andrewb435/gameKey-STL/Thumb Cluster/gameKey_Thumb_Rail.stl

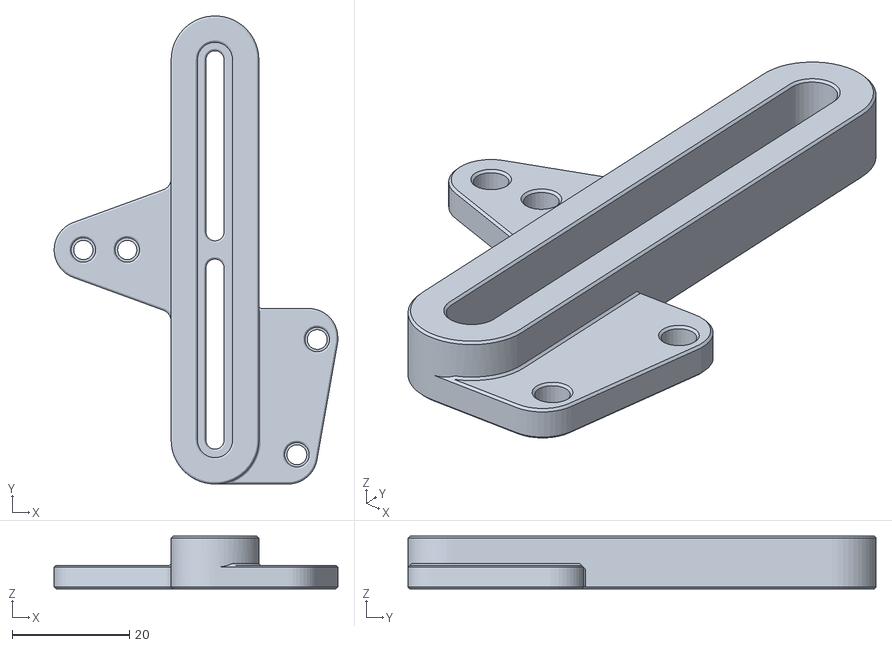
[picture p16: CAD file, 2022-02-08]
Thumb Cluster/gameKey_Thumb_Rail.stl
48.5 x 80.0 x 9.00
