andrewb435/gameKey-STL/Base & Palmrest/gameKey_Finger_SliderMount_Index.stl

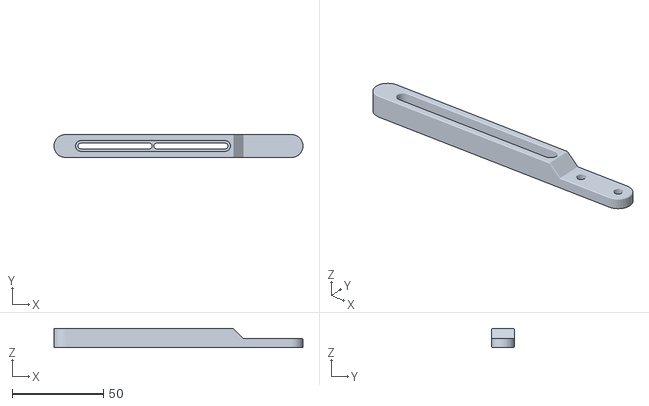
[picture p17: CAD file, 2022-02-08]
Base & Palmrest/gameKey_Finger_SliderMount_Index.stl
136.8 x 12.6 x 10.5
