andrewb435/gameKey-STL/Fingers/gameKey_Finger_Addon_IndexB.stl

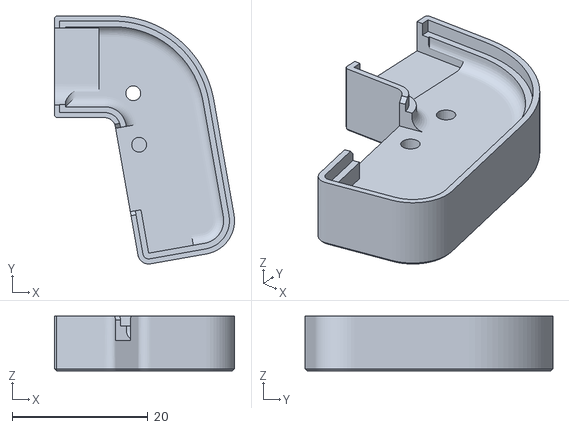
[picture p18: CAD file, 2022-02-08]
Fingers/gameKey_Finger_Addon_IndexB.stl
26.6 x 36.6 x 8.10
