andrewb435/gameKey-STL/Base & Palmrest/gameKey_Finger_SliderMount_Middle.stl

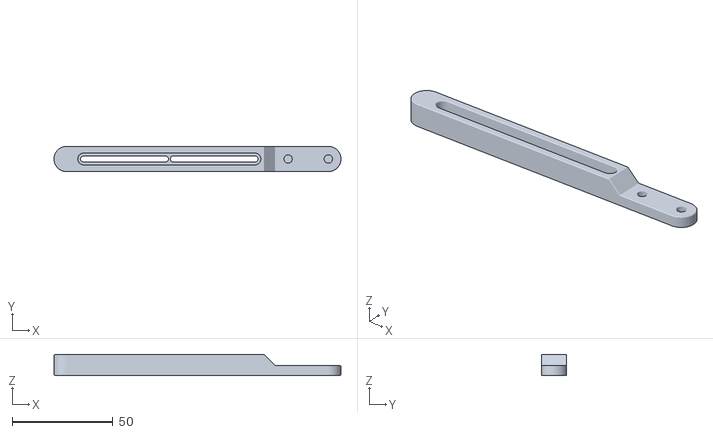
[picture p19: CAD file, 2022-02-08]
Base & Palmrest/gameKey_Finger_SliderMount_Middle.stl
142.6 x 12.6 x 10.5
