andrewb435/gameKey-STL/Fingers/gameKey_Finger_Addon_IndexA.stl

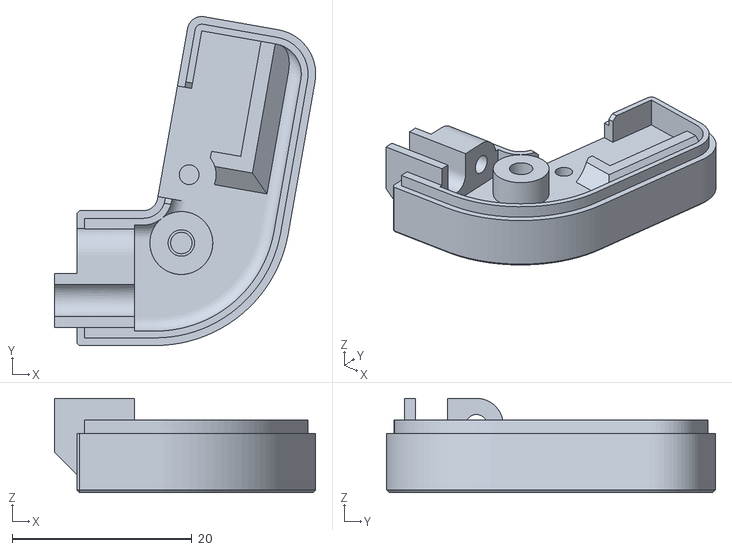
[picture p20: CAD file, 2022-02-08]
Fingers/gameKey_Finger_Addon_IndexA.stl
29.1 x 36.6 x 10.5
