andrewb435/gameKey-STL/Thumb Cluster/gameKey_ThumbCluster_JS5208-Stick.stl

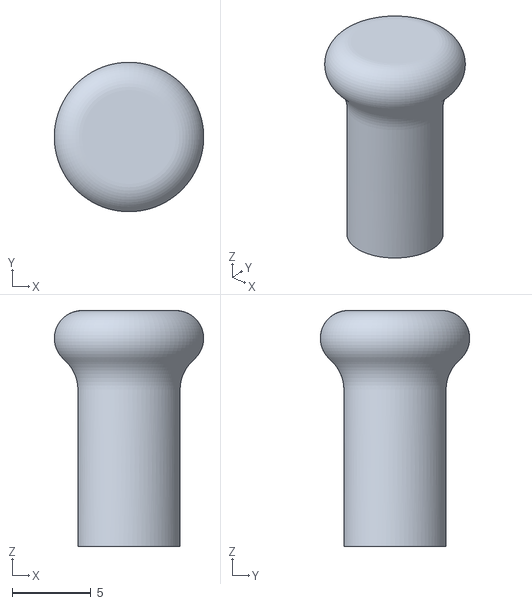
[picture p21: CAD file, 2022-02-08]
Thumb Cluster/gameKey_ThumbCluster_JS5208-Stick.stl
9.49 x 9.50 x 15.0
