andrewb435/gameKey-STL/Base & Palmrest/gameKey_Finger_SliderMount_Ring.stl

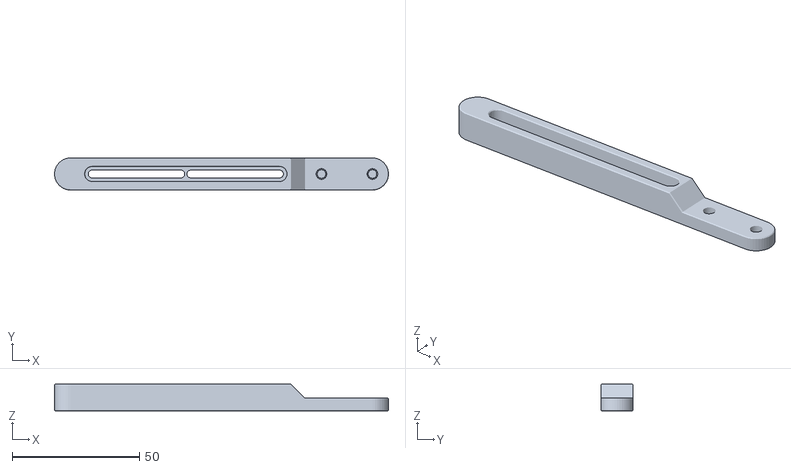
[picture p22: CAD file, 2022-02-08]
Base & Palmrest/gameKey_Finger_SliderMount_Ring.stl
131.1 x 12.6 x 10.5
