andrewb435/gameKey-STL/Thumb Cluster/gameKey_ThumbCluster_Body.stl

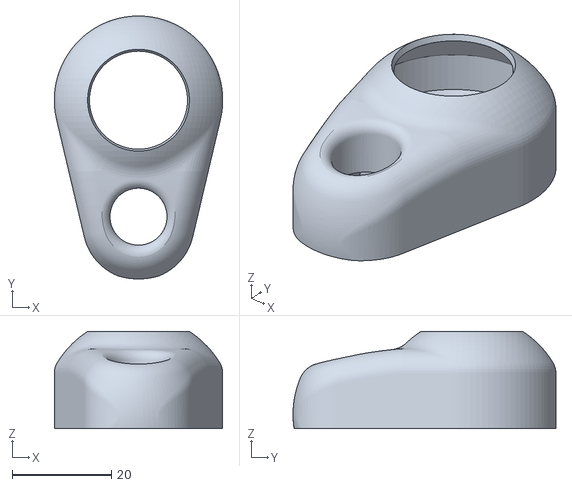
[picture p23: CAD file, 2022-02-08]
Thumb Cluster/gameKey_ThumbCluster_Body.stl
34.0 x 53.1 x 19.6
