andrewb435/gameKey-STL/Thumb Cluster/gameKey_ThumbCluster_Back.stl

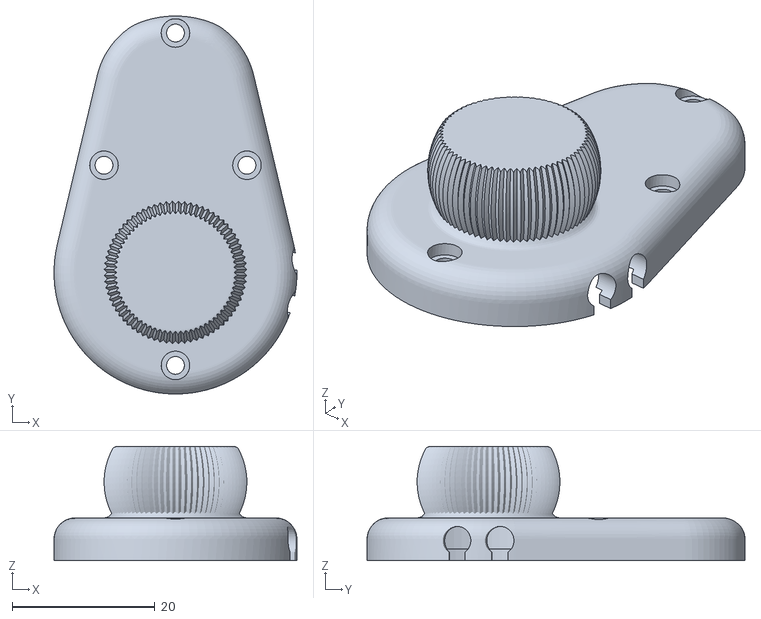
[picture p24: CAD file, 2022-02-08]
Thumb Cluster/gameKey_ThumbCluster_Back.stl
34.0 x 52.9 x 16.0
