andrewb435/gameKey-STL/Fingers/gameKey_Finger_PaddleLarge.stl

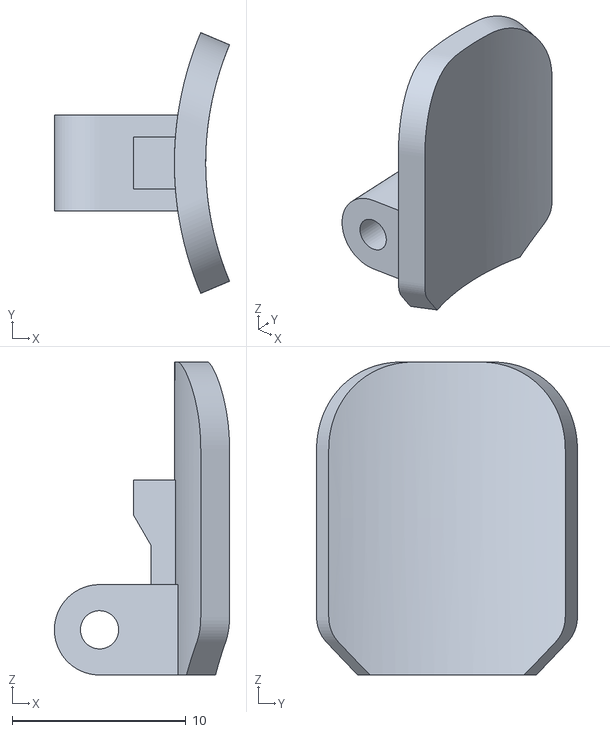
[picture p25: CAD file, 2022-02-08]
Fingers/gameKey_Finger_PaddleLarge.stl
10.1 x 15.0 x 18.0
